rodrjm/AdquisidorBiopotenciales/Firmware/lpc_board_ciaa_edu_4337/src/board.c

/*
 * Copyright(C) NXP Semiconductors, 2012
 * All rights reserved.
 *
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
 * Permission to use, copy, modify, and distribute this software and its
 * documentation is hereby granted, under NXP Semiconductors' and its
 * licensor's relevant copyrights in the software, without fee, provided that it
 * is used in conjunction with NXP Semiconductors microcontrollers.  This
 * copyright, permission, and disclaimer notice must appear in all copies of
 * this code.
 */

#include "board.h"
#include "string.h"

/** @ingroup BOARD_NGX_XPLORER_18304330
 * @{
 */

/* SDIO Data pin configuration bits */
#define SDIO_DAT_PINCFG (SCU_MODE_HIGHSPEEDSLEW_EN | SCU_MODE_INBUFF_EN | SCU_MODE_ZIF_DIS | SCU_MODE_PULLUP | SCU_MODE_FUNC7)

#define GPIO_BUTTONS_SIZE   (sizeof(GpioButtons) / sizeof(struct gpio_t))

/*****************************************************************************
 * Public types/enumerations/variables
 ****************************************************************************/

/* System configuration variables used by chip driver */
const uint32_t ExtRateIn = 0;
const uint32_t OscRateIn = 12000000;

struct gpio_t {
   uint8_t port;
   uint8_t pin;
};

typedef struct {
   uint8_t port;
   uint8_t pin;
} io_port_t;

static const struct gpio_t GpioButtons[] = {{0, 4}, {0, 8}, {0, 9}, {1, 9}};
static const io_port_t gpioLEDBits[] = {{0, 14}, {1, 11}, {1, 12}, {5, 0}, {5, 1}, {5, 2}};
static uint32_t lcd_cfg_val;

void Board_UART_Init(LPC_USART_T *pUART)
{
   Chip_SCU_PinMuxSet(0x6, 4, (SCU_MODE_INACT | SCU_MODE_FUNC2));                  /* P6,4 : UART0_TXD */
   Chip_SCU_PinMuxSet(0x2, 1, (SCU_MODE_INACT | SCU_MODE_INBUFF_EN | SCU_MODE_ZIF_DIS | SCU_MODE_FUNC1));/* P2.1 : UART0_RXD */
}

/* Initialize debug output via UART for board */
void Board_Debug_Init(void)
{
#if defined(DEBUG_UART)
   Board_UART_Init(DEBUG_UART);

   Chip_UART_Init(DEBUG_UART);
   Chip_UART_SetBaudFDR(DEBUG_UART, 115200);
   Chip_UART_ConfigData(DEBUG_UART, UART_LCR_WLEN8 | UART_LCR_SBS_1BIT | UART_LCR_PARITY_DIS);

   /* Enable UART Transmit */
   Chip_UART_TXEnable(DEBUG_UART);
#endif
}

/* Sends a character on the UART */
void Board_UARTPutChar(char ch)
{
#if defined(DEBUG_UART)
   /* Wait for space in FIFO */
   while ((Chip_UART_ReadLineStatus(DEBUG_UART) & UART_LSR_THRE) == 0) {}
   Chip_UART_SendByte(DEBUG_UART, (uint8_t) ch);
#endif
}

/* Gets a character from the UART, returns EOF if no character is ready */
int Board_UARTGetChar(void)
{
#if defined(DEBUG_UART)
   if (Chip_UART_ReadLineStatus(DEBUG_UART) & UART_LSR_RDR) {
       return (int) Chip_UART_ReadByte(DEBUG_UART);
   }
#endif
   return EOF;
}

/* Outputs a string on the debug UART */
void Board_UARTPutSTR(const char *str)
{
#if defined(DEBUG_UART)
   while (*str != '\0') {
       Board_UARTPutChar(*str++);
   }
#endif
}

static void Board_LED_Init()
{
   uint32_t idx;

   for (idx = 0; idx < (sizeof(gpioLEDBits) / sizeof(io_port_t)); ++idx) {
       /* Set pin direction and init to off */
       Chip_GPIO_SetPinDIROutput(LPC_GPIO_PORT, gpioLEDBits[idx].port, gpioLEDBits[idx].pin);
       Chip_GPIO_SetPinState(LPC_GPIO_PORT, gpioLEDBits[idx].port, gpioLEDBits[idx].pin, (bool) false);
   }
}

void Board_LED_Set(uint8_t LEDNumber, bool On)
{
   if (LEDNumber < (sizeof(gpioLEDBits) / sizeof(io_port_t)))
        Chip_GPIO_SetPinState(LPC_GPIO_PORT, gpioLEDBits[LEDNumber].port, gpioLEDBits[LEDNumber].pin, (bool) !On);
}

bool Board_LED_Test(uint8_t LEDNumber)
{
   if (LEDNumber < (sizeof(gpioLEDBits) / sizeof(io_port_t)))
       return (bool) !Chip_GPIO_GetPinState(LPC_GPIO_PORT, gpioLEDBits[LEDNumber].port, gpioLEDBits[LEDNumber].pin);

   return false;
}

void Board_LED_Toggle(uint8_t LEDNumber)
{
   Board_LED_Set(LEDNumber, !Board_LED_Test(LEDNumber));
}

static void Board_TEC_Init()
{
   for (uint32_t i = 0; i < GPIO_BUTTONS_SIZE; ++i) {
      const struct gpio_t *io = &GpioButtons[i];
      Chip_GPIO_SetPinDIRInput(LPC_GPIO_PORT, io->port, io->pin);
   }
}

bool Board_TEC_GetStatus(uint8_t button)
{
   if (button >= GPIO_BUTTONS_SIZE) {
      return false;
   }

   return Chip_GPIO_GetPinState(LPC_GPIO_PORT, GpioButtons[button].port, GpioButtons[button].pin);
}

/* Returns the MAC address assigned to this board */
void Board_ENET_GetMacADDR(uint8_t *mcaddr)
{
   uint8_t boardmac[] = {0x00, 0x60, 0x37, 0x12, 0x34, 0x56};

   memcpy(mcaddr, boardmac, 6);
}

/* Set up and initialize all required blocks and functions related to the
   board hardware */
void Board_Init(void)
{
   /* Sets up DEBUG UART */
   DEBUGINIT();

   /* Initializes GPIO */
   Chip_GPIO_Init(LPC_GPIO_PORT);

   /* Initialize LEDs */
   Board_LED_Init();
   Board_TEC_Init();
   Chip_ENET_RMIIEnable(LPC_ETHERNET);
}

void Board_I2C_Init(I2C_ID_T id)
{
   if (id == I2C1) {
       /* Configure pin function for I2C1*/
       Chip_SCU_PinMuxSet(0x2, 3, (SCU_MODE_ZIF_DIS | SCU_MODE_INBUFF_EN | SCU_MODE_FUNC1));       /* P2.3 : I2C1_SDA */
       Chip_SCU_PinMuxSet(0x2, 4, (SCU_MODE_ZIF_DIS | SCU_MODE_INBUFF_EN | SCU_MODE_FUNC1));       /* P2.4 : I2C1_SCL */
   } else {
       Chip_SCU_I2C0PinConfig(I2C0_STANDARD_FAST_MODE);
   }
}

void Board_SDMMC_Init(void)
{
   Chip_SCU_PinMuxSet(0x1, 9, SDIO_DAT_PINCFG);    /* P1.9 connected to SDIO_D0 */
   Chip_SCU_PinMuxSet(0x1, 10, SDIO_DAT_PINCFG);   /* P1.10 connected to SDIO_D1 */
   Chip_SCU_PinMuxSet(0x1, 11, SDIO_DAT_PINCFG);   /* P1.11 connected to SDIO_D2 */
   Chip_SCU_PinMuxSet(0x1, 12, SDIO_DAT_PINCFG);   /* P1.12 connected to SDIO_D3 */

   Chip_SCU_ClockPinMuxSet(2, (SCU_MODE_INACT | SCU_MODE_INBUFF_EN | SCU_MODE_FUNC4)); /* CLK2 connected to SDIO_CLK */
   Chip_SCU_PinMuxSet(0x1, 6, SDIO_DAT_PINCFG);    /* P1.6 connected to SDIO_CMD */
   Chip_SCU_PinMuxSet(0x1, 13, (SCU_MODE_INBUFF_EN | SCU_MODE_FUNC7)); /* P1.13 connected to SDIO_CD */
}

void Board_SSP_Init(LPC_SSP_T *pSSP)
{
   if (pSSP == LPC_SSP1) {
       Chip_SCU_PinMuxSet(0x1, 5, (SCU_PINIO_FAST | SCU_MODE_FUNC5));  /* P1.5 => SSEL1 */
       Chip_SCU_PinMuxSet(0xF, 4, (SCU_PINIO_FAST | SCU_MODE_FUNC0));  /* PF.4 => SCK1 */
       Chip_SCU_PinMuxSet(0x1, 4, (SCU_MODE_INACT | SCU_MODE_INBUFF_EN | SCU_MODE_ZIF_DIS | SCU_MODE_FUNC5)); /* P1.4 => MOSI1 */
       Chip_SCU_PinMuxSet(0x1, 3, (SCU_MODE_INACT | SCU_MODE_INBUFF_EN | SCU_MODE_ZIF_DIS | SCU_MODE_FUNC5)); /* P1.3 => MISO1 */
   } else {
       return;
   }
}

/* Initialize DAC interface for the board */
void Board_DAC_Init(LPC_DAC_T *pDAC)
{
   Chip_SCU_DAC_Analog_Config();
}

/**
 * @}
 */
