rodrjm/AdquisidorBiopotenciales/Firmware/app/inc/biopotenciales.h

#ifndef _BIOPOTENCIALES_H_
#define _BIOPOTENCIALES_H_


/*==================[inclusions]=============================================*/
#include "Drv_Devices.h"
#include "GPIO.h"
#include "ADS131E08.h"



/*==================[cplusplus]==============================================*/

#ifdef __cplusplus
extern "C" {
#endif

/*==================[macros]=================================================*/

/*==================[typedef]================================================*/

/*==================[external data declaration]==============================*/

/*==================[external functions declaration]=========================*/

/** @brief main function
 * @return main function should never return
 */
int main(void);

/*==================[cplusplus]==============================================*/

#ifdef __cplusplus
}
#endif

/** @} doxygen end group definition */
/*==================[end of file]============================================*/
#endif /* #ifndef _BIOPOTENCIALES_H_ */
